ElPercha/PLsi/hard/CPU/v0/board/pictures/PLsi_00.jpg

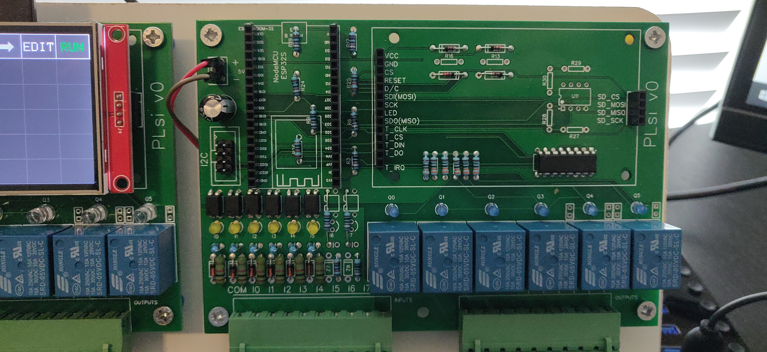
hard/CPU/v0/board/pictures/PLsi_00.jpg
