ElPercha/PLsi/hard/CPU/v0/board/pictures/PLsi_01.jpg

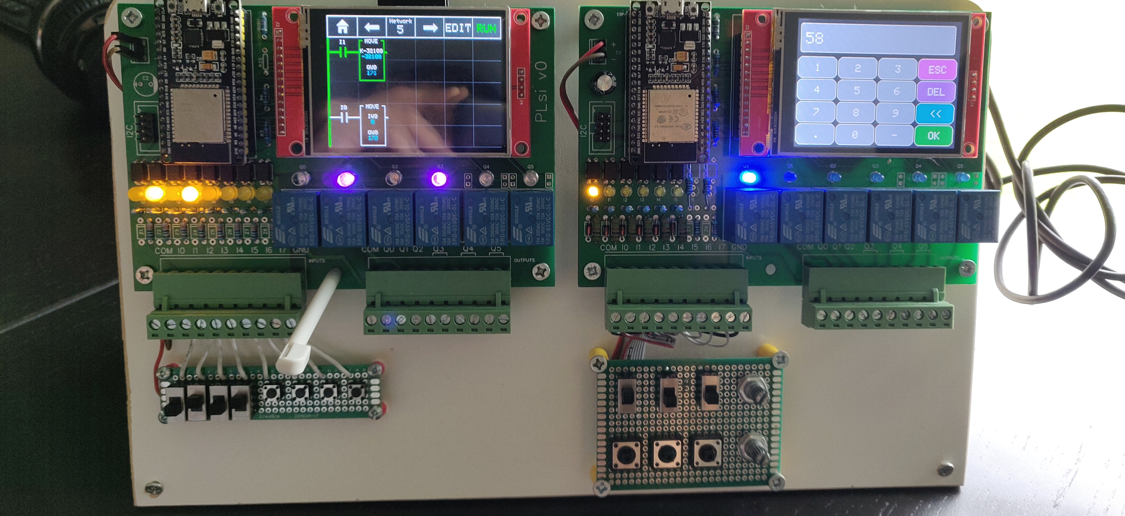
hard/CPU/v0/board/pictures/PLsi_01.jpg
