ElPercha/PLsi/hard/CPU/v0/board/pictures/PLsi_02.jpg

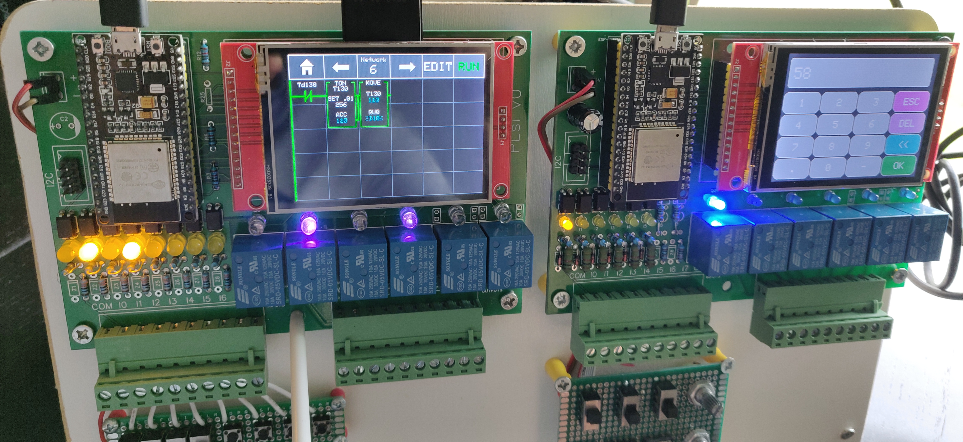
hard/CPU/v0/board/pictures/PLsi_02.jpg
