ElPercha/PLsi/hard/CPU/v0/board/pictures/PLsi_03.jpg

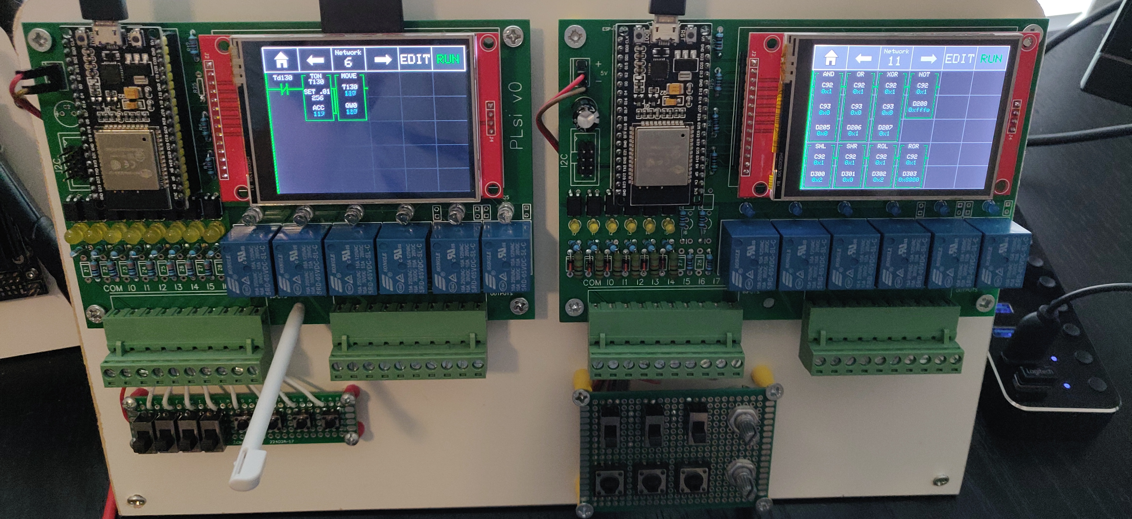
hard/CPU/v0/board/pictures/PLsi_03.jpg
