ElPercha/PLsi/hard/CPU/v0/housing/pictures/1.png

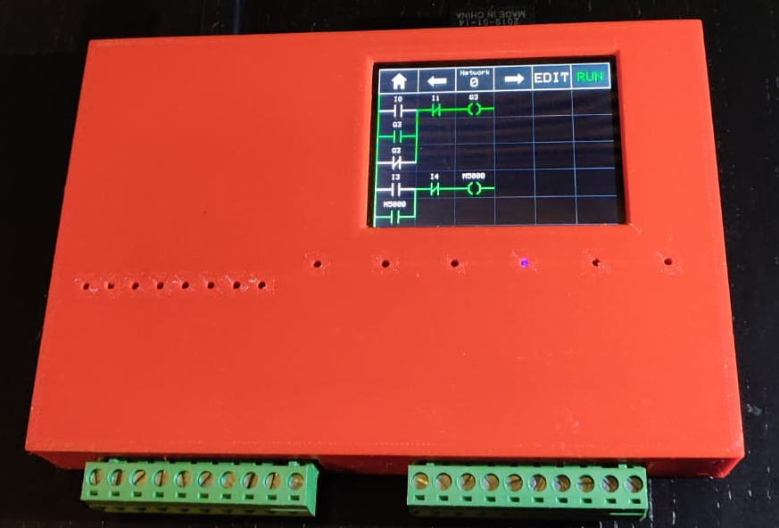
hard/CPU/v0/housing/pictures/1.png
