ElPercha/PLsi/hard/CPU/v0/housing/pictures/2.png

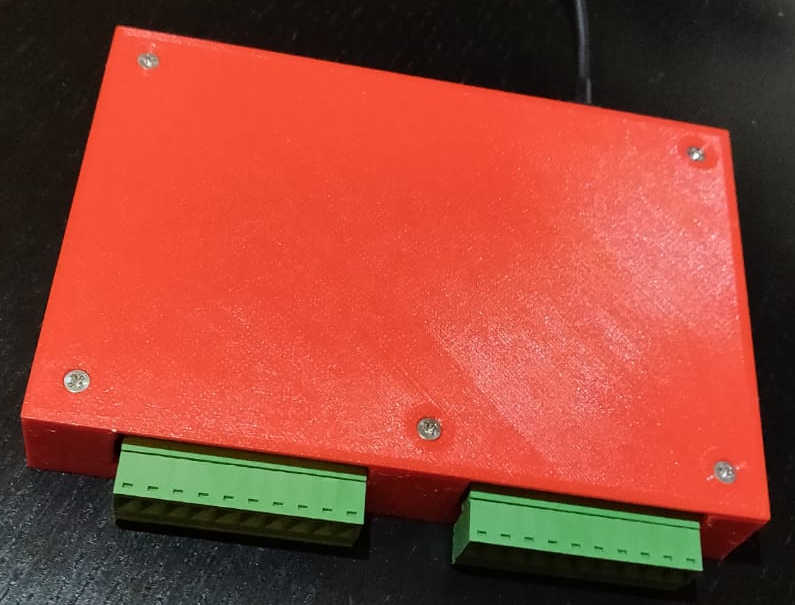
hard/CPU/v0/housing/pictures/2.png
