ElPercha/PLsi/hard/CPU/v0/housing/pictures/3.png

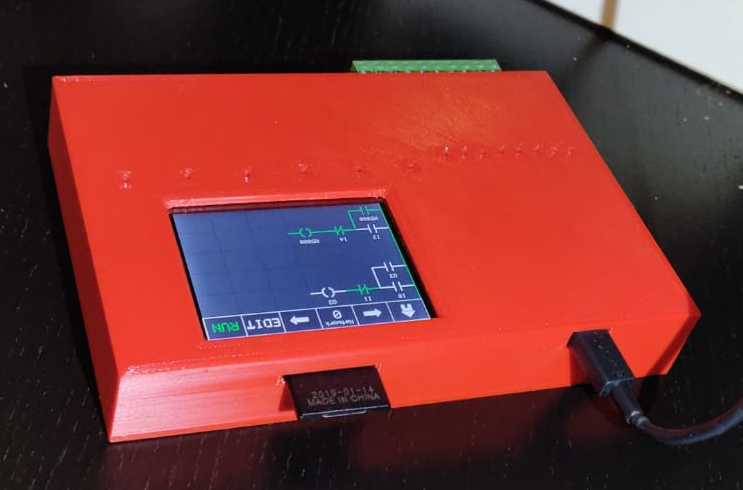
hard/CPU/v0/housing/pictures/3.png
