ElPercha/PLsi/hard/CPU/v0/housing/pictures/4.png

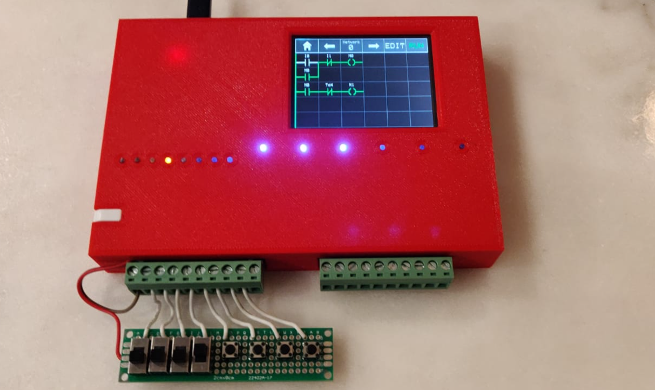
hard/CPU/v0/housing/pictures/4.png
