ElPercha/PLsi/hard/CPU/v0/housing/pictures/din rail mount 2.png

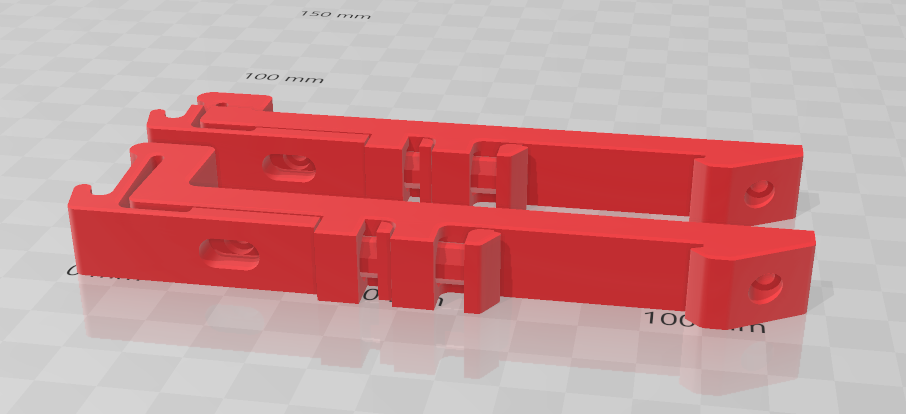
hard/CPU/v0/housing/pictures/din rail mount 2.png
