ElPercha/PLsi/hard/CPU/v0/housing/pictures/PLsi v0 - Board.png

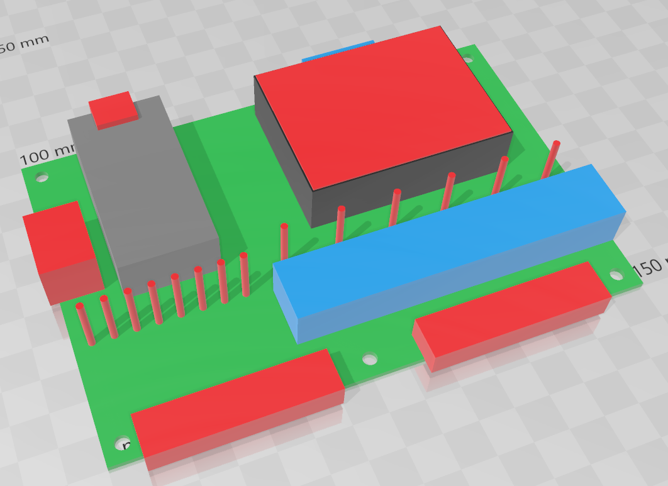
hard/CPU/v0/housing/pictures/PLsi v0 - Board.png
