ElPercha/PLsi/hard/CPU/v0/housing/pictures/PLsi v0 - Housing Base.png

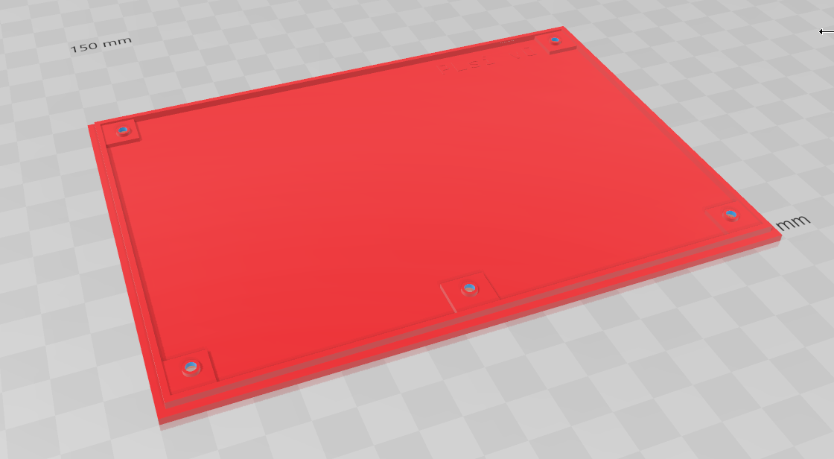
hard/CPU/v0/housing/pictures/PLsi v0 - Housing Base.png
