ElPercha/PLsi/hard/CPU/v0/housing/pictures/PLsi v0 - Housing Cover with Touch Pen.png

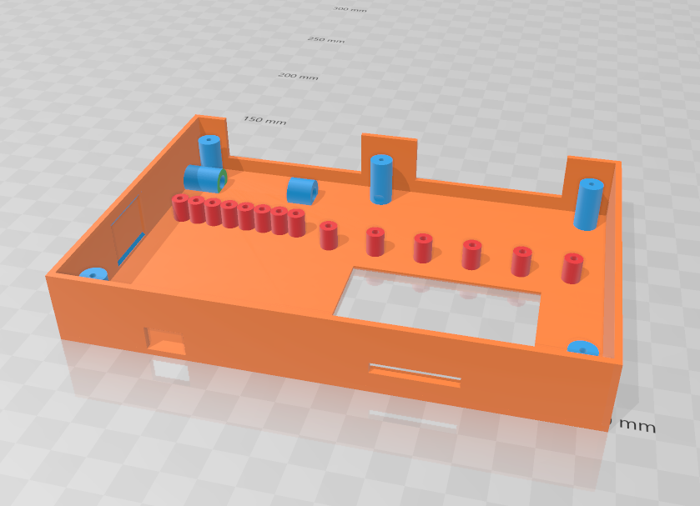
hard/CPU/v0/housing/pictures/PLsi v0 - Housing Cover with Touch Pen.png
