ElPercha/PLsi/doc/ongoing/Auxiliars/pictures for manuals/Assembly pictures/1 - Materials/1.jpeg

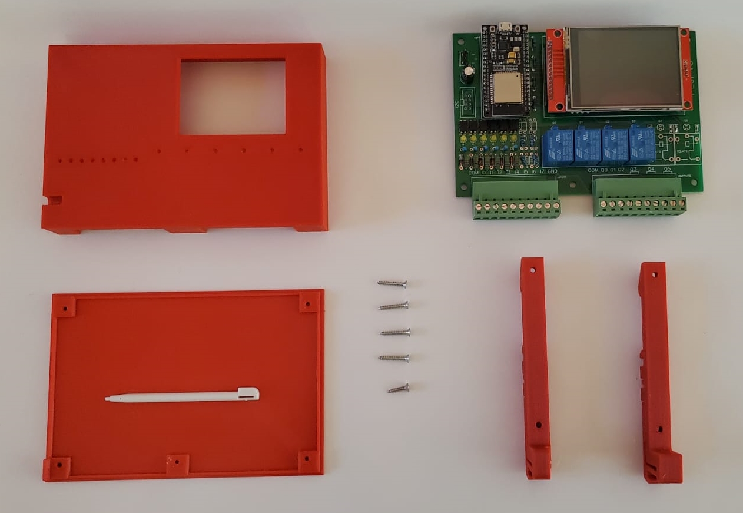
doc/ongoing/Auxiliars/pictures for manuals/Assembly pictures/1 - Materials/1.jpeg
