ElPercha/PLsi/doc/ongoing/Auxiliars/pictures for manuals/Assembly pictures/1 - Materials/2.jpeg

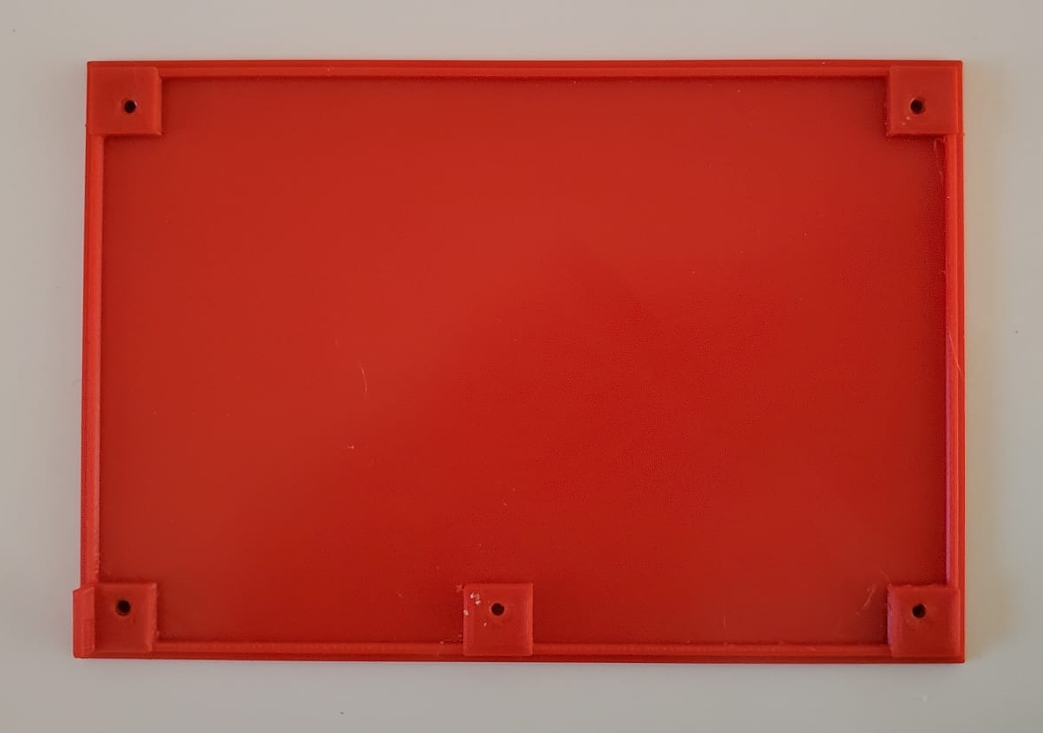
doc/ongoing/Auxiliars/pictures for manuals/Assembly pictures/1 - Materials/2.jpeg
