ElPercha/PLsi/doc/ongoing/Auxiliars/pictures for manuals/Assembly pictures/1 - Materials/4.jpeg

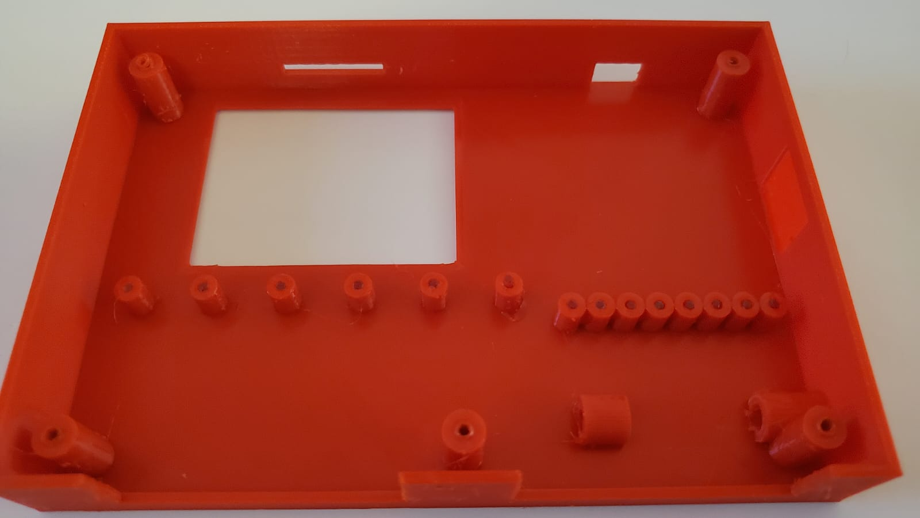
doc/ongoing/Auxiliars/pictures for manuals/Assembly pictures/1 - Materials/4.jpeg
