ElPercha/PLsi/doc/ongoing/Auxiliars/pictures for manuals/Assembly pictures/1 - Materials/5.jpeg

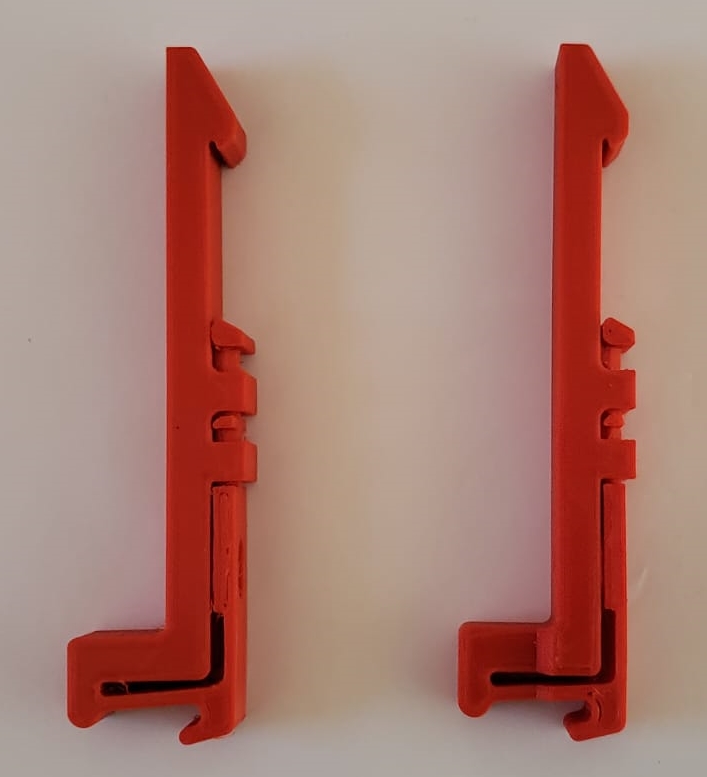
doc/ongoing/Auxiliars/pictures for manuals/Assembly pictures/1 - Materials/5.jpeg
