ElPercha/PLsi/doc/ongoing/Auxiliars/pictures for manuals/1.png

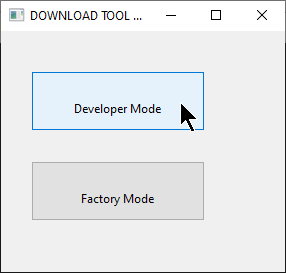
doc/ongoing/Auxiliars/pictures for manuals/1.png
