ElPercha/PLsi/doc/ongoing/Auxiliars/pictures for manuals/3.png

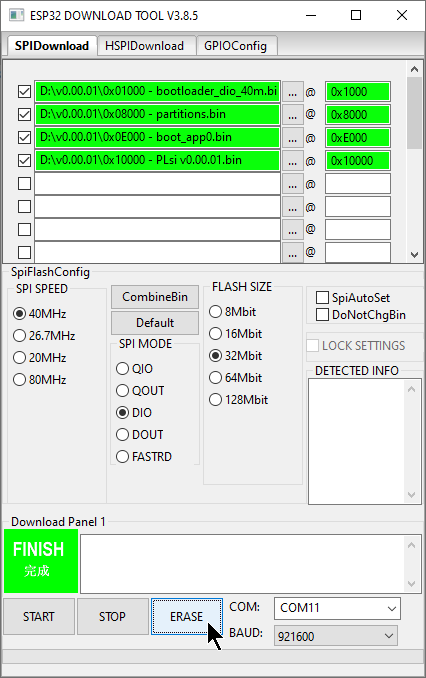
doc/ongoing/Auxiliars/pictures for manuals/3.png
