ElPercha/PLsi/doc/ongoing/Auxiliars/pictures for manuals/4.png

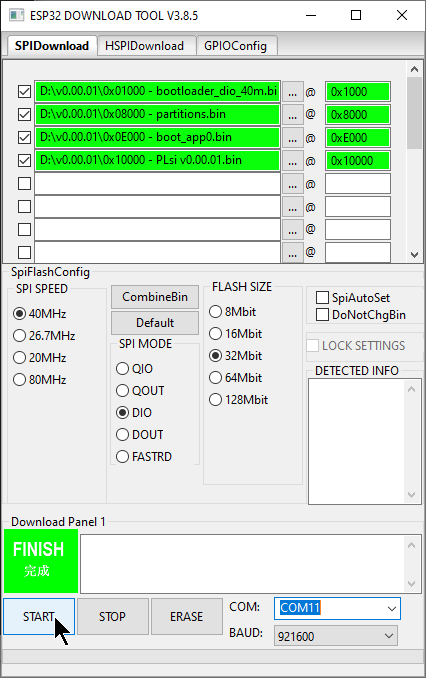
doc/ongoing/Auxiliars/pictures for manuals/4.png
