ElPercha/PLsi/doc/ongoing/Auxiliars/pictures for manuals/5.png

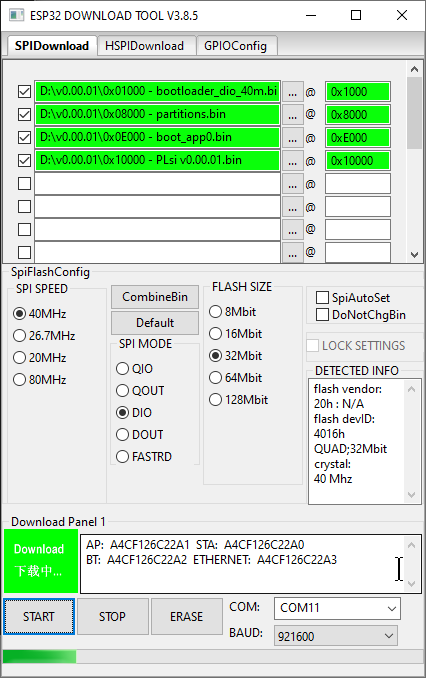
doc/ongoing/Auxiliars/pictures for manuals/5.png
