ElPercha/PLsi/doc/ongoing/Auxiliars/pictures for manuals/6.png

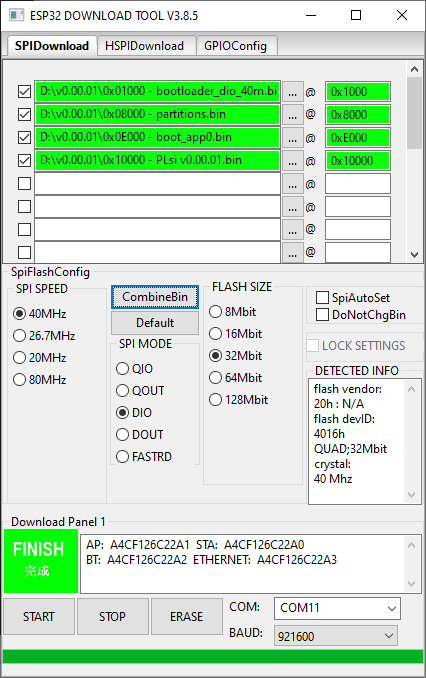
doc/ongoing/Auxiliars/pictures for manuals/6.png
