ElPercha/PLsi/doc/ongoing/Auxiliars/pictures for manuals/ADC_10Bit.png

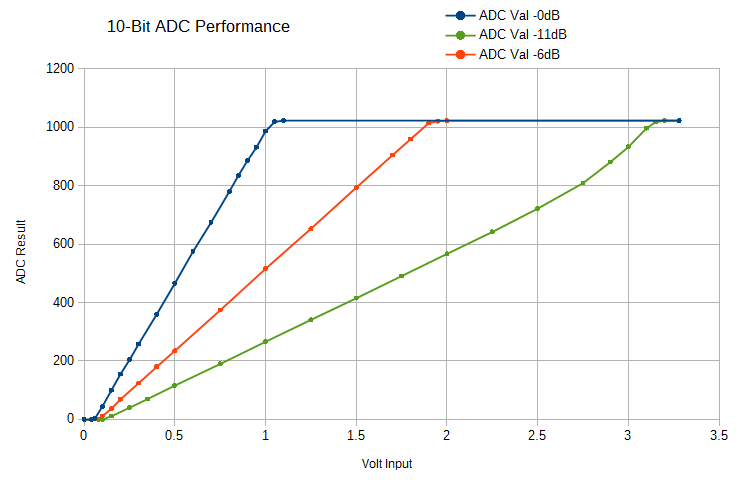
doc/ongoing/Auxiliars/pictures for manuals/ADC_10Bit.png
