ElPercha/PLsi/doc/ongoing/Auxiliars/pictures for manuals/analog unl2003 detail.PNG

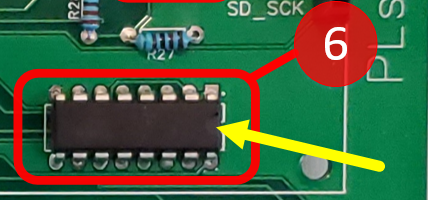
doc/ongoing/Auxiliars/pictures for manuals/analog unl2003 detail.PNG
