ElPercha/PLsi/doc/ongoing/Auxiliars/pictures for manuals/analogdivider.PNG

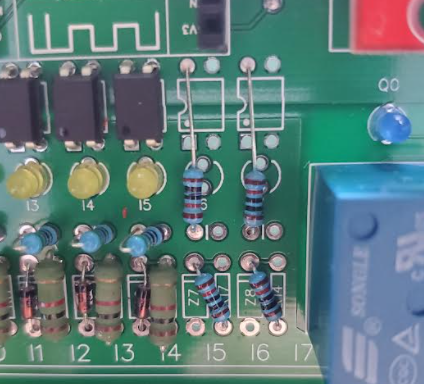
doc/ongoing/Auxiliars/pictures for manuals/analogdivider.PNG
