ElPercha/PLsi/doc/ongoing/Auxiliars/pictures for manuals/Assembly pictures/2 - Acrylic bars/5.jpeg

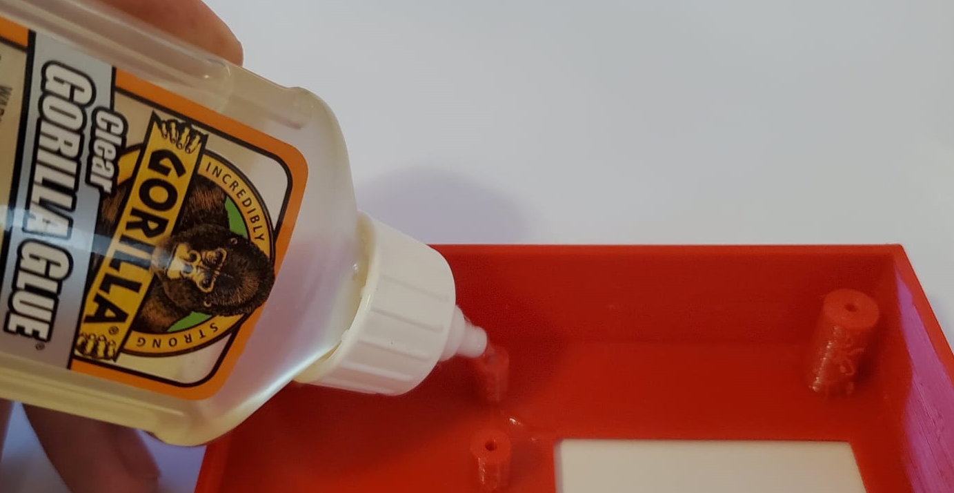
doc/ongoing/Auxiliars/pictures for manuals/Assembly pictures/2 - Acrylic bars/5.jpeg
