ElPercha/PLsi/doc/ongoing/Auxiliars/pictures for manuals/Assembly pictures/3 - assembly/4.jpeg

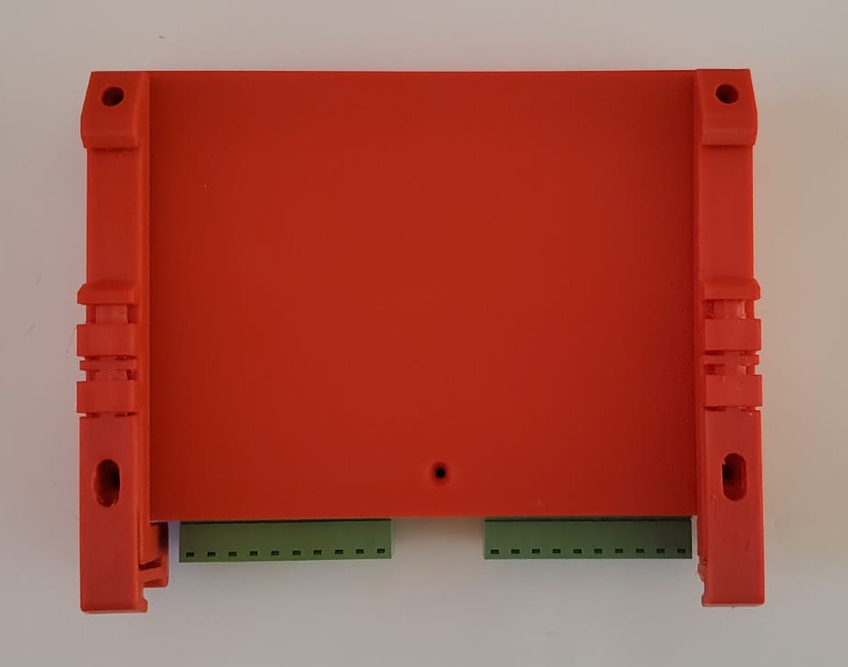
doc/ongoing/Auxiliars/pictures for manuals/Assembly pictures/3 - assembly/4.jpeg
