ElPercha/PLsi/doc/ongoing/Auxiliars/pictures for manuals/auxV.PNG

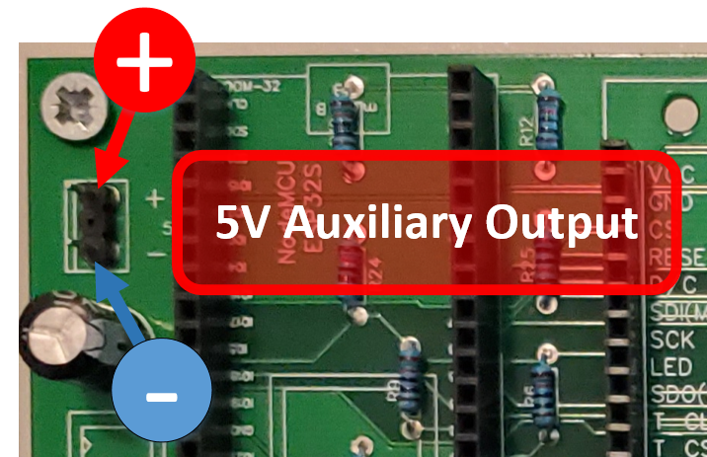
doc/ongoing/Auxiliars/pictures for manuals/auxV.PNG
