ElPercha/PLsi/doc/ongoing/Auxiliars/pictures for manuals/bar.jpg

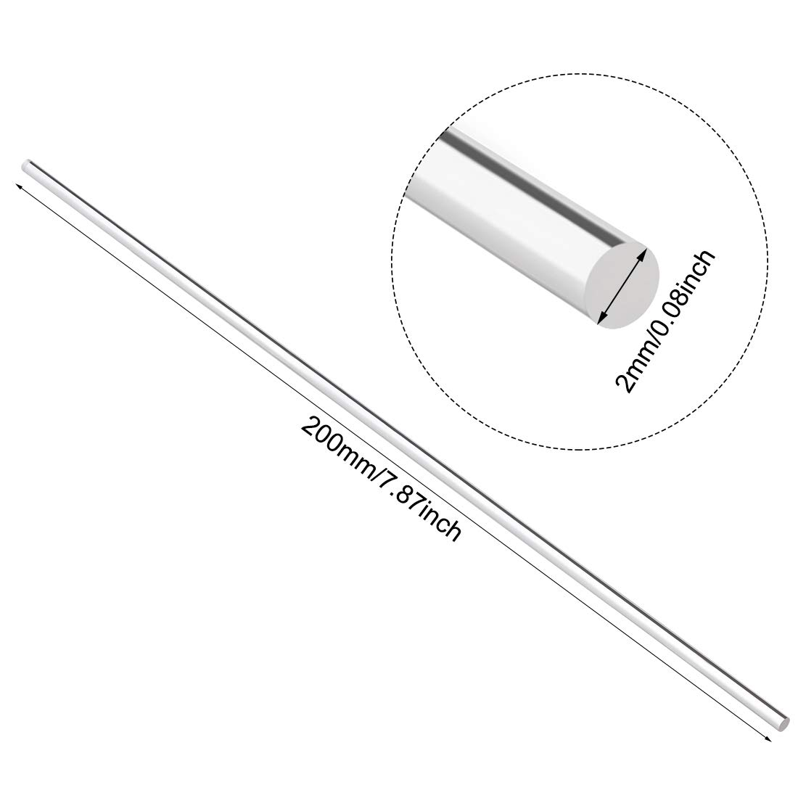
doc/ongoing/Auxiliars/pictures for manuals/bar.jpg
