ElPercha/PLsi/doc/ongoing/Auxiliars/pictures for manuals/capacitor detail.PNG

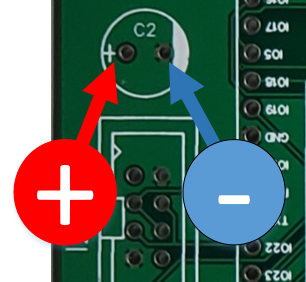
doc/ongoing/Auxiliars/pictures for manuals/capacitor detail.PNG
