ElPercha/PLsi/doc/ongoing/Auxiliars/pictures for manuals/click.png

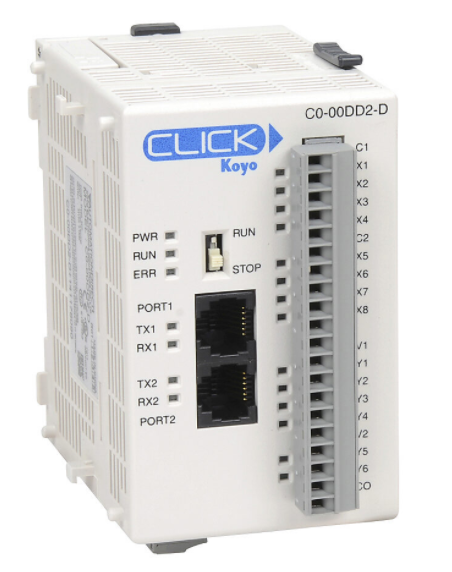
doc/ongoing/Auxiliars/pictures for manuals/click.png
