ElPercha/PLsi/doc/ongoing/Auxiliars/pictures for manuals/Dioded detail analog.PNG

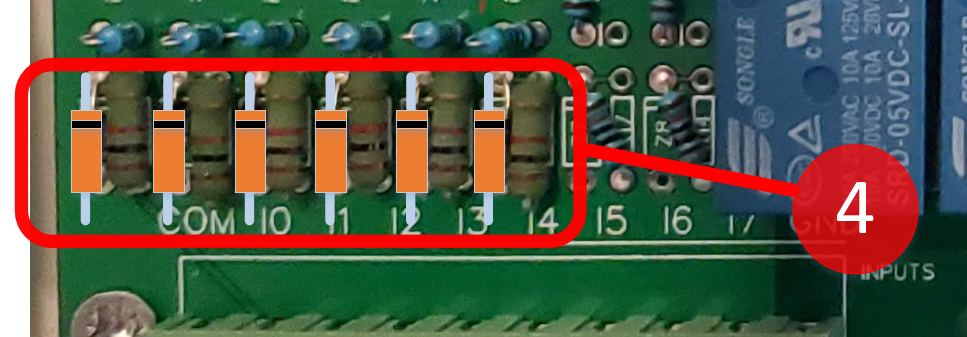
doc/ongoing/Auxiliars/pictures for manuals/Dioded detail analog.PNG
