ElPercha/PLsi/doc/ongoing/Auxiliars/pictures for manuals/Dioded detail digital.PNG

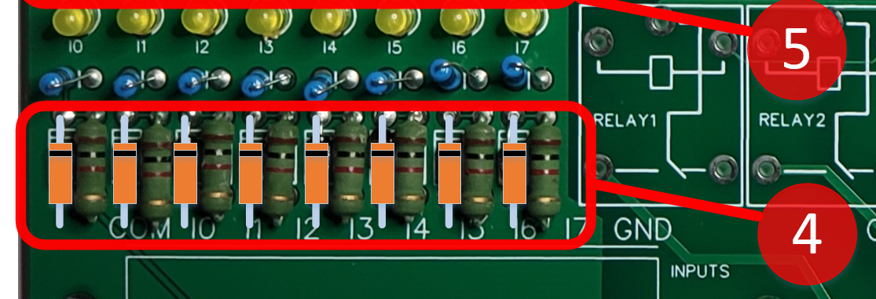
doc/ongoing/Auxiliars/pictures for manuals/Dioded detail digital.PNG
