ElPercha/PLsi/doc/ongoing/Auxiliars/pictures for manuals/Dioded detail.PNG

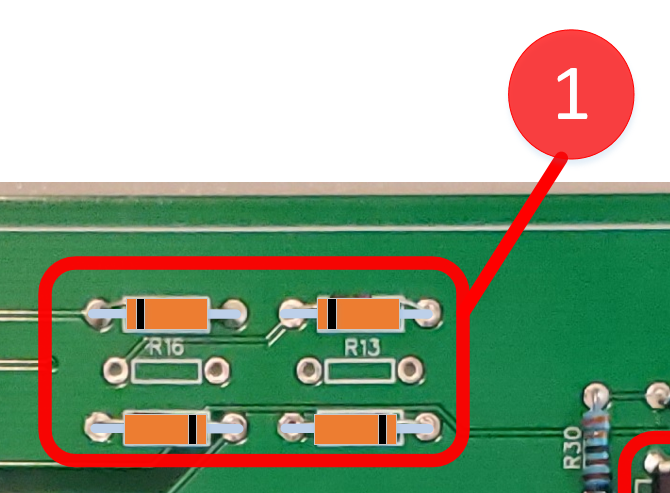
doc/ongoing/Auxiliars/pictures for manuals/Dioded detail.PNG
