ElPercha/PLsi/doc/ongoing/Auxiliars/pictures for manuals/display welding.PNG

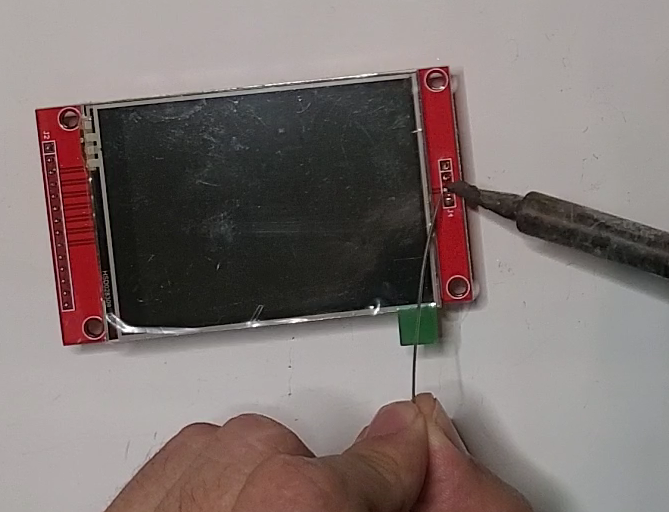
doc/ongoing/Auxiliars/pictures for manuals/display welding.PNG
