ElPercha/PLsi/doc/ongoing/Auxiliars/pictures for manuals/download2.PNG

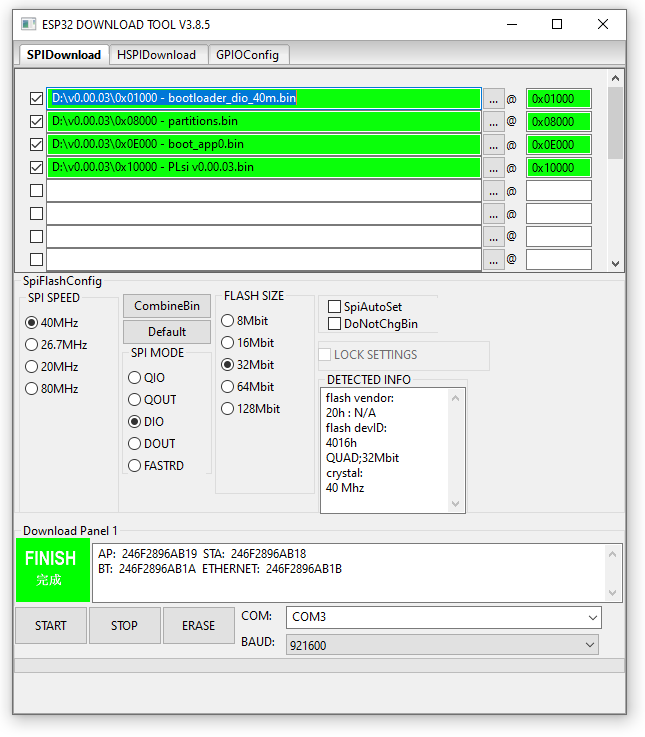
doc/ongoing/Auxiliars/pictures for manuals/download2.PNG
