ElPercha/PLsi/doc/ongoing/Auxiliars/pictures for manuals/download3.PNG

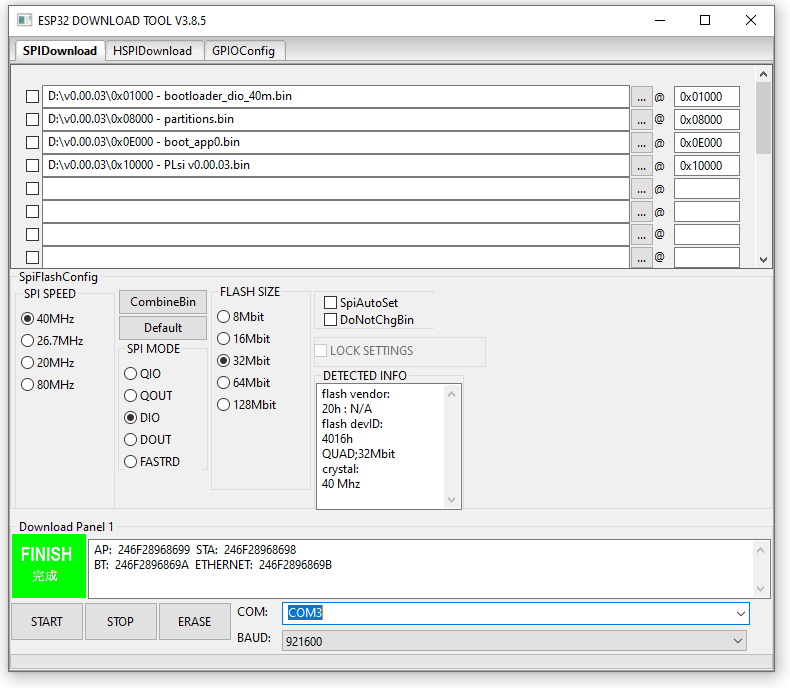
doc/ongoing/Auxiliars/pictures for manuals/download3.PNG
