ElPercha/PLsi/doc/ongoing/Auxiliars/pictures for manuals/download4.PNG

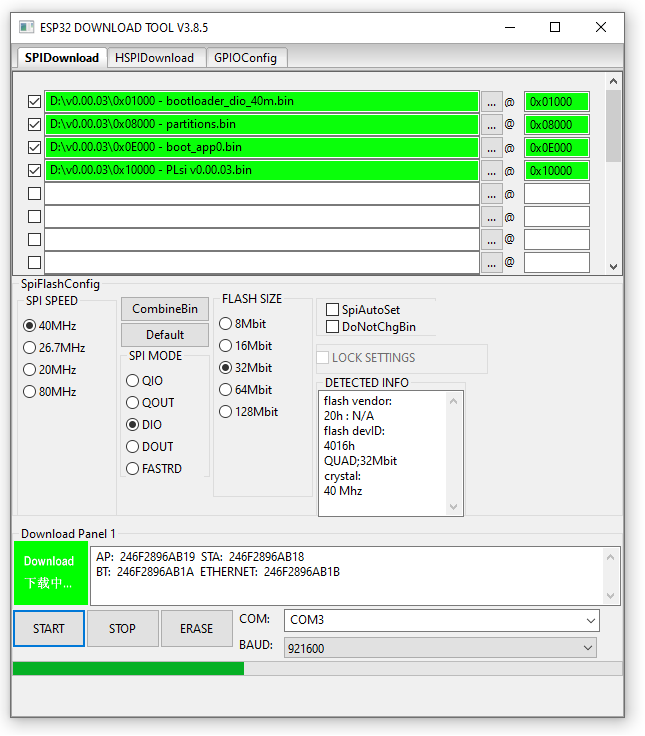
doc/ongoing/Auxiliars/pictures for manuals/download4.PNG
