ElPercha/PLsi/doc/ongoing/Auxiliars/pictures for manuals/download5.PNG

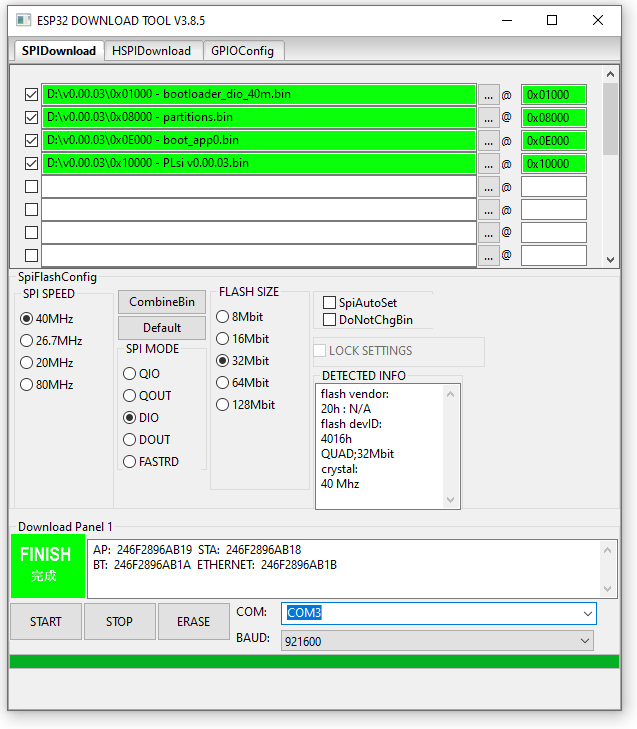
doc/ongoing/Auxiliars/pictures for manuals/download5.PNG
