ElPercha/PLsi/doc/ongoing/Auxiliars/pictures for manuals/download6.PNG

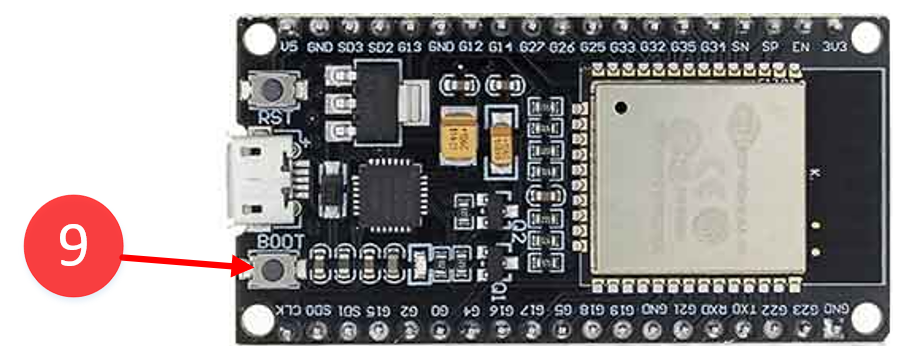
doc/ongoing/Auxiliars/pictures for manuals/download6.PNG
