ElPercha/PLsi/doc/ongoing/Auxiliars/pictures for manuals/download7.PNG

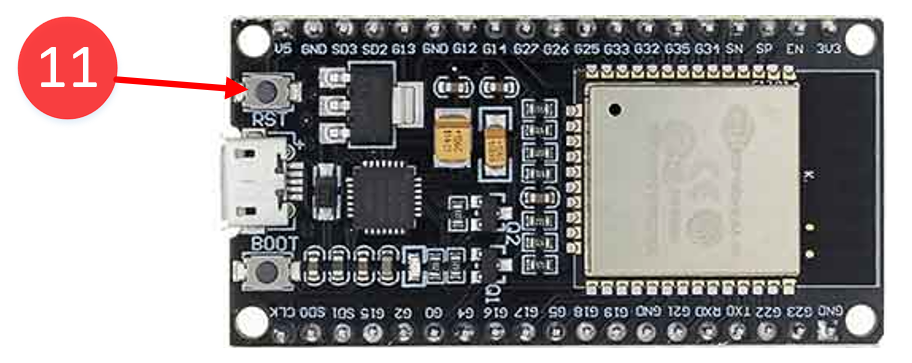
doc/ongoing/Auxiliars/pictures for manuals/download7.PNG
