ElPercha/PLsi/doc/ongoing/Auxiliars/pictures for manuals/download espressiff.PNG

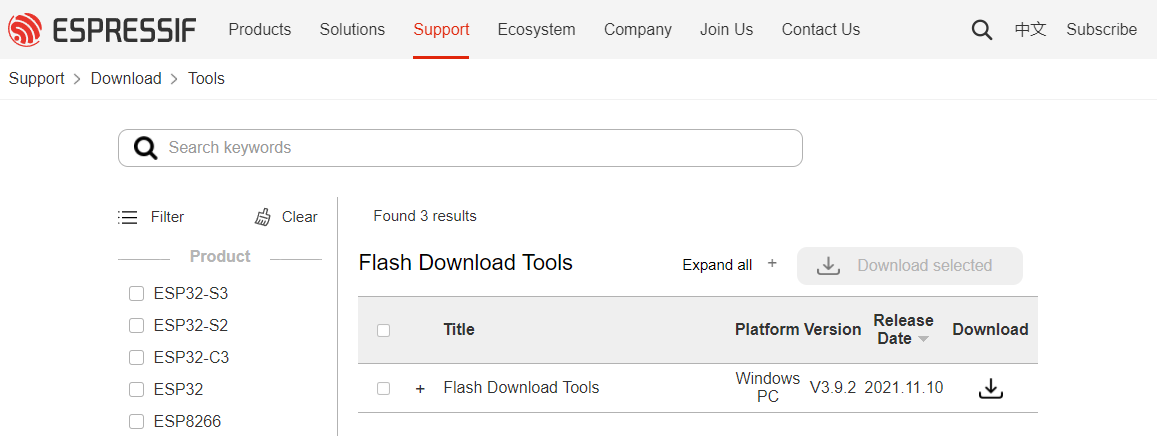
doc/ongoing/Auxiliars/pictures for manuals/download espressiff.PNG
