ElPercha/PLsi/doc/ongoing/Auxiliars/pictures for manuals/download tool.PNG

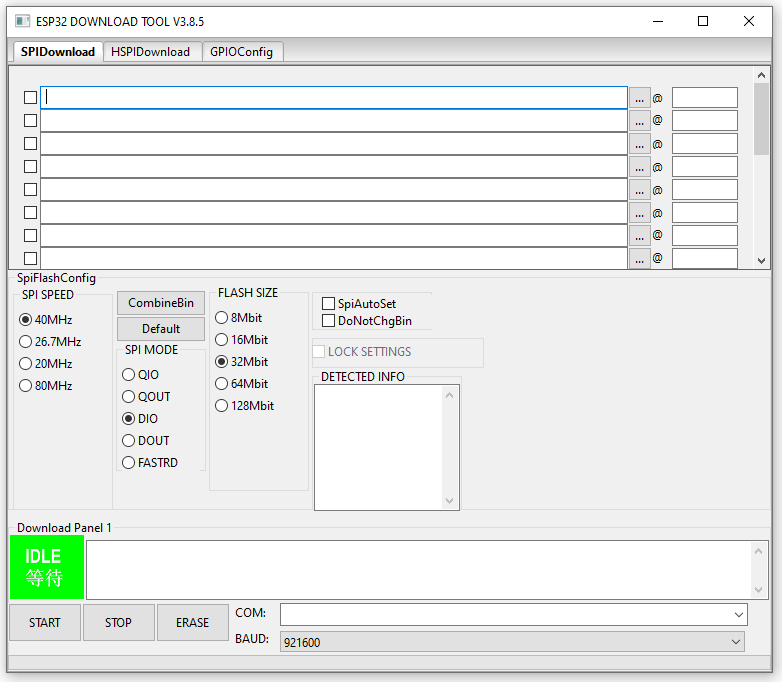
doc/ongoing/Auxiliars/pictures for manuals/download tool.PNG
