ElPercha/PLsi/doc/ongoing/Auxiliars/pictures for manuals/drawing 1.PNG

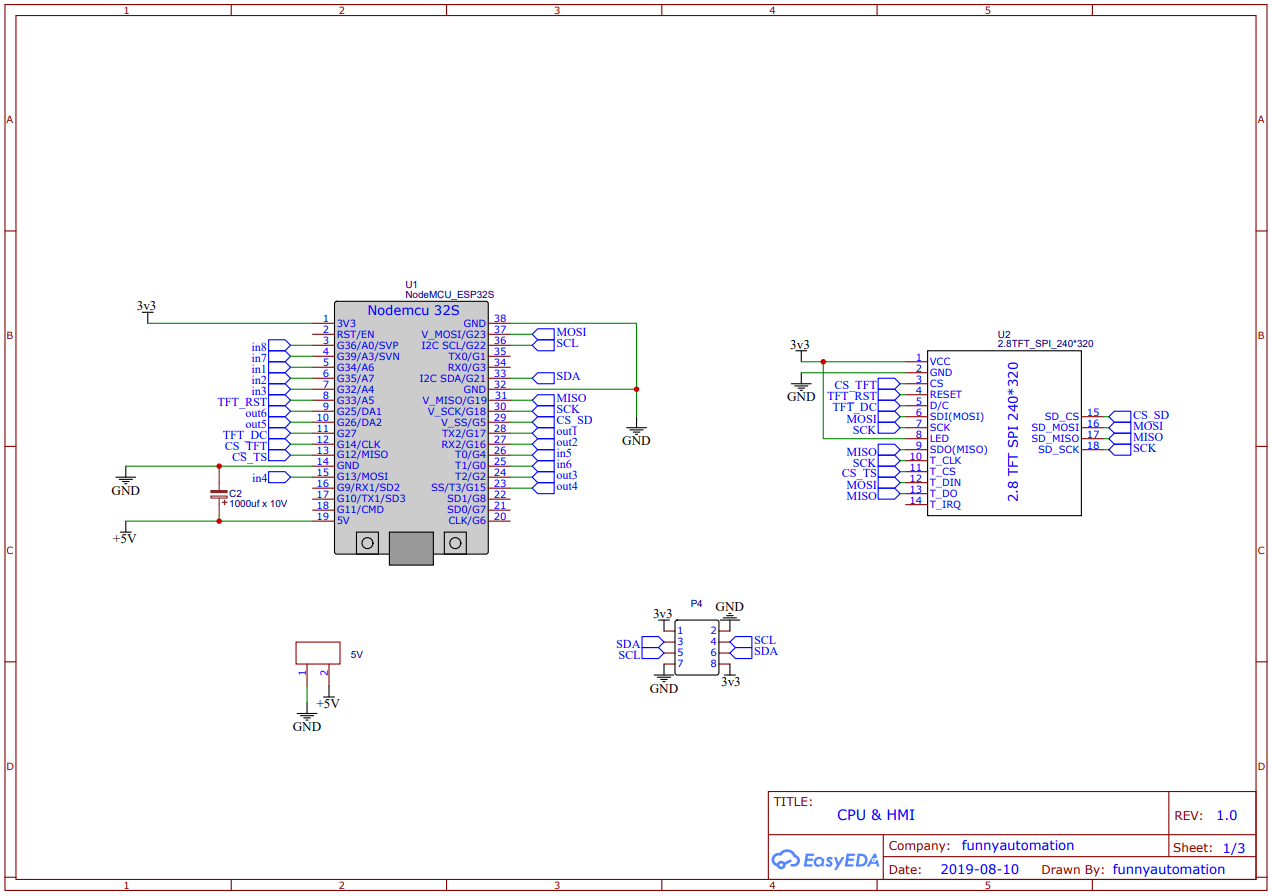
doc/ongoing/Auxiliars/pictures for manuals/drawing 1.PNG
