ElPercha/PLsi/doc/ongoing/Auxiliars/pictures for manuals/drawing 3.PNG

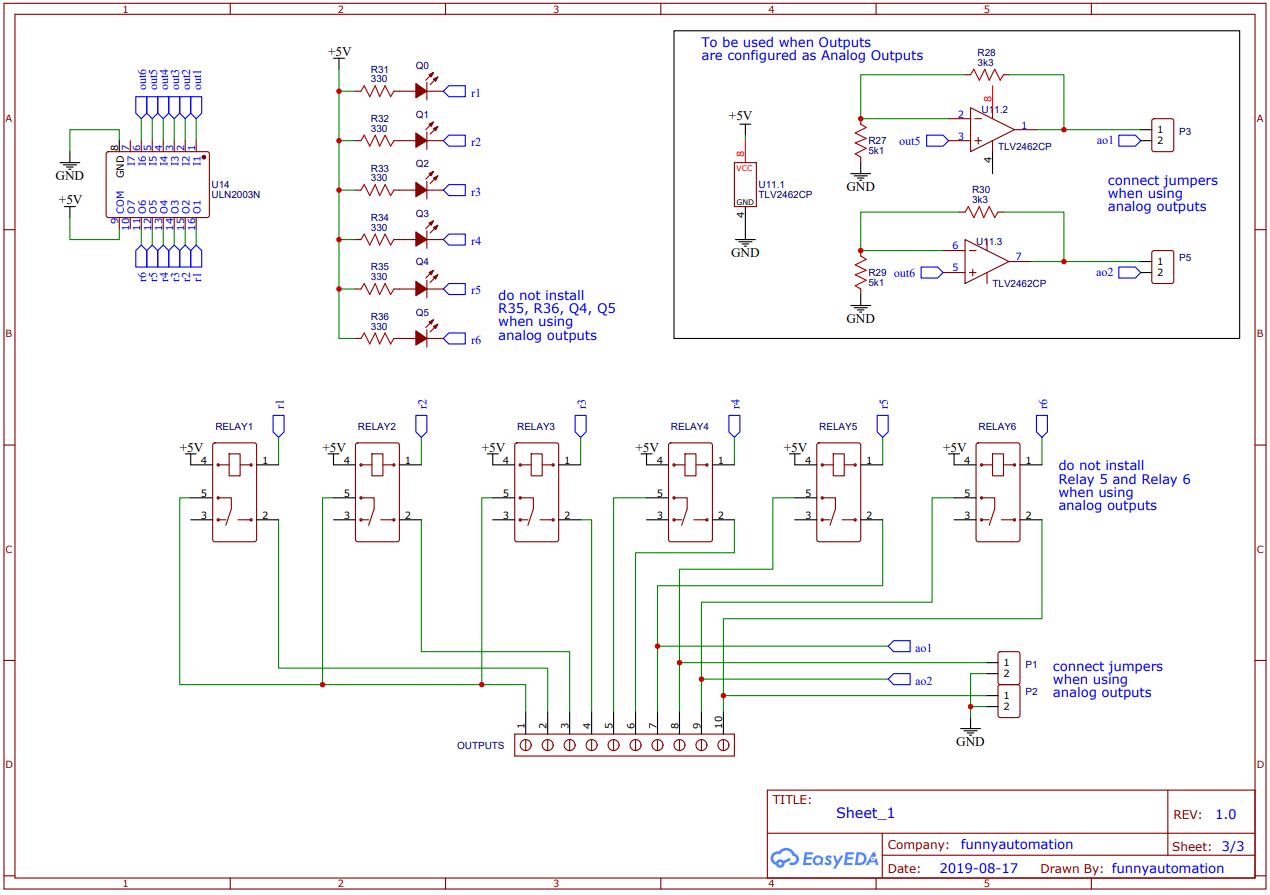
doc/ongoing/Auxiliars/pictures for manuals/drawing 3.PNG
