ElPercha/PLsi/doc/ongoing/Auxiliars/pictures for manuals/dupont female1.PNG

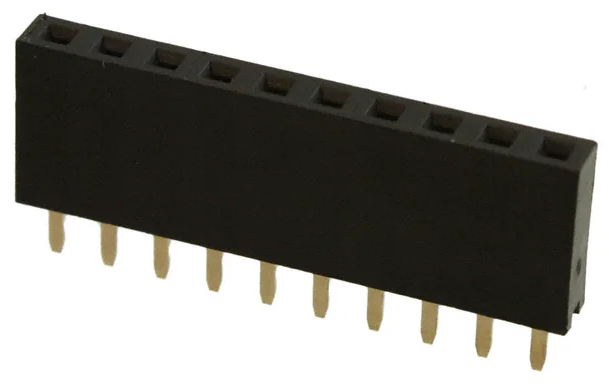
doc/ongoing/Auxiliars/pictures for manuals/dupont female1.PNG
