ElPercha/PLsi/doc/ongoing/Auxiliars/pictures for manuals/dupont female.PNG

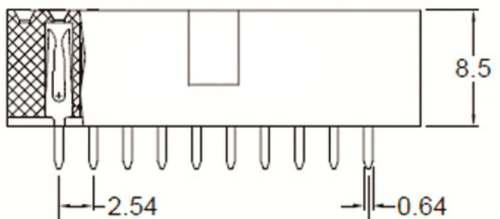
doc/ongoing/Auxiliars/pictures for manuals/dupont female.PNG
