ElPercha/PLsi/doc/ongoing/Auxiliars/pictures for manuals/esp32.PNG

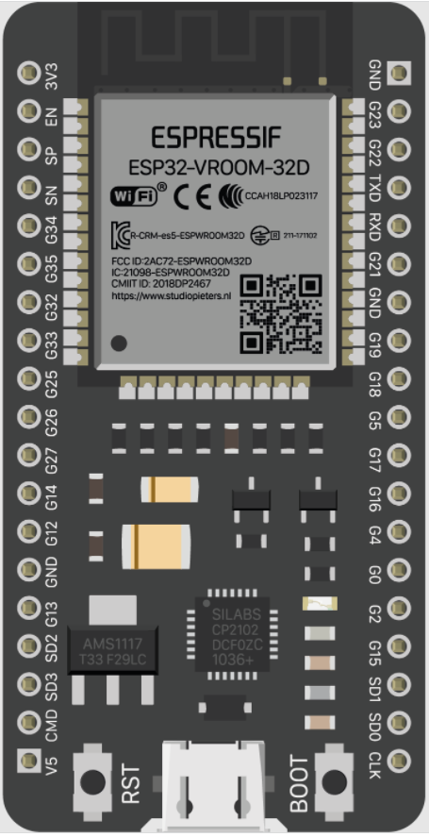
doc/ongoing/Auxiliars/pictures for manuals/esp32.PNG
