ElPercha/PLsi/doc/ongoing/Auxiliars/pictures for manuals/esp321.PNG

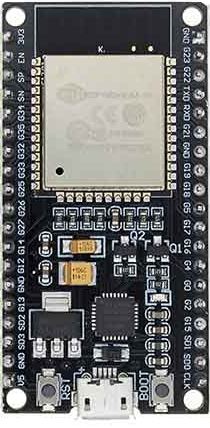
doc/ongoing/Auxiliars/pictures for manuals/esp321.PNG
