ElPercha/PLsi/doc/ongoing/Auxiliars/pictures for manuals/espressif.png

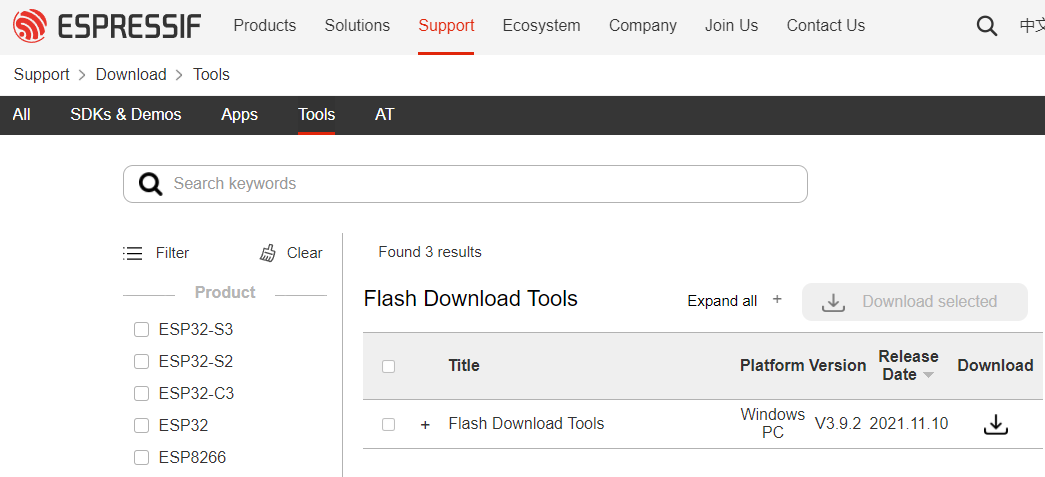
doc/ongoing/Auxiliars/pictures for manuals/espressif.png
