ElPercha/PLsi/doc/ongoing/Auxiliars/pictures for manuals/flashtool.PNG

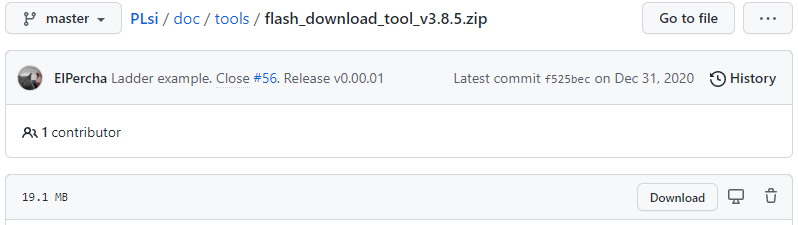
doc/ongoing/Auxiliars/pictures for manuals/flashtool.PNG
