ElPercha/PLsi/doc/ongoing/Auxiliars/pictures for manuals/led.PNG

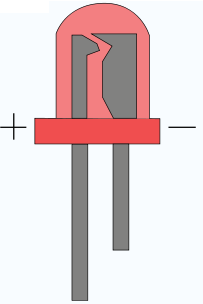
doc/ongoing/Auxiliars/pictures for manuals/led.PNG
