ElPercha/PLsi/doc/ongoing/Auxiliars/pictures for manuals/opamp detail.PNG

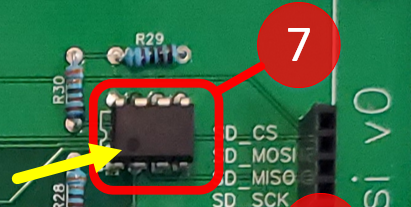
doc/ongoing/Auxiliars/pictures for manuals/opamp detail.PNG
