ElPercha/PLsi/doc/ongoing/Auxiliars/pictures for manuals/optionsdigital.PNG

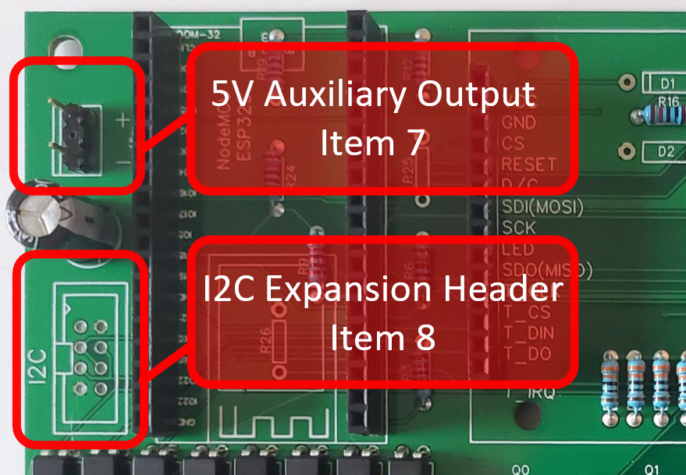
doc/ongoing/Auxiliars/pictures for manuals/optionsdigital.PNG
