ElPercha/PLsi/doc/ongoing/Auxiliars/pictures for manuals/optoanalogdetail.PNG

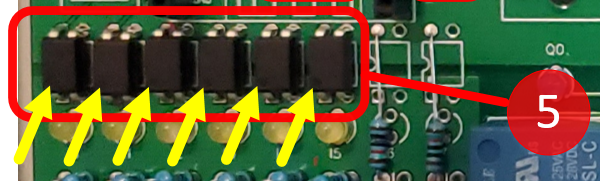
doc/ongoing/Auxiliars/pictures for manuals/optoanalogdetail.PNG
