ElPercha/PLsi/doc/ongoing/Auxiliars/pictures for manuals/PC817 Details.PNG

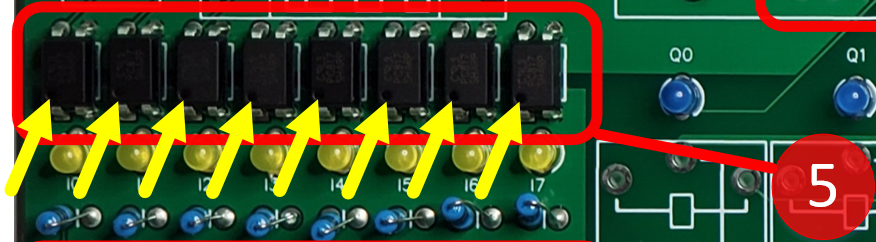
doc/ongoing/Auxiliars/pictures for manuals/PC817 Details.PNG
