ElPercha/PLsi/doc/ongoing/Auxiliars/pictures for manuals/plsi flash tool.PNG

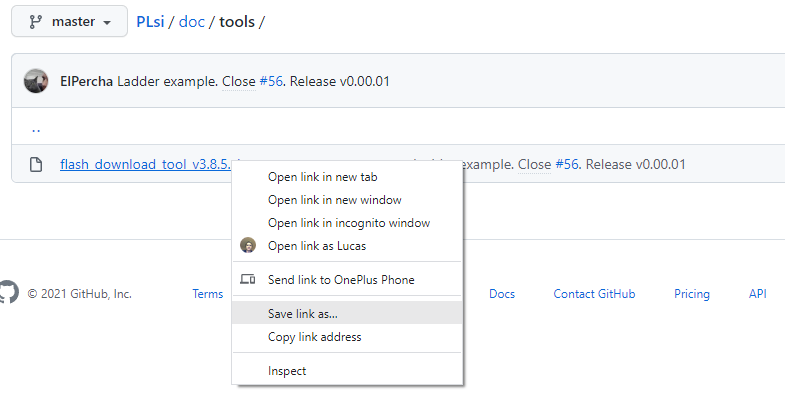
doc/ongoing/Auxiliars/pictures for manuals/plsi flash tool.PNG
