ElPercha/PLsi/doc/ongoing/Auxiliars/pictures for manuals/screw1.png

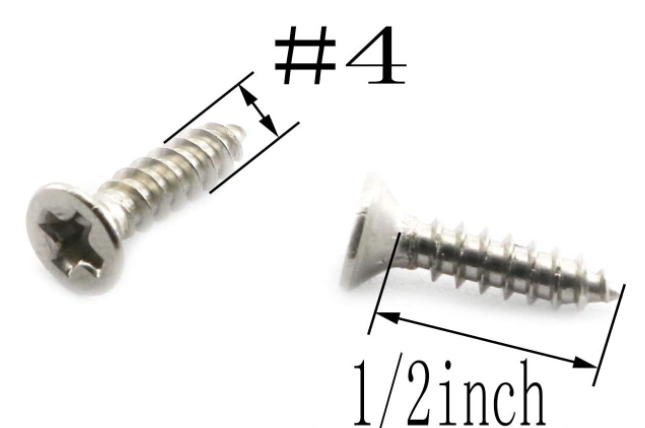
doc/ongoing/Auxiliars/pictures for manuals/screw1.png
