ElPercha/PLsi/doc/ongoing/Auxiliars/pictures for manuals/UNL2003 detail.PNG

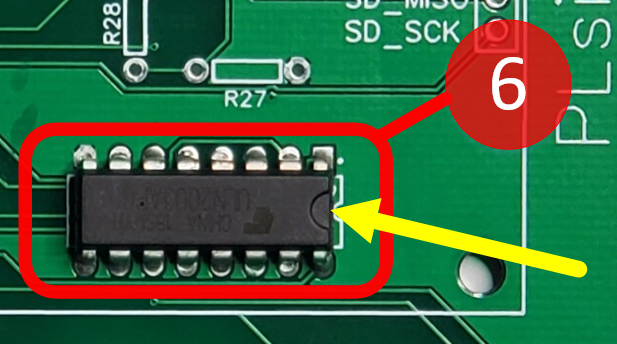
doc/ongoing/Auxiliars/pictures for manuals/UNL2003 detail.PNG
