ElPercha/PLsi/doc/ongoing/Auxiliars/pictures for manuals/unzip.PNG

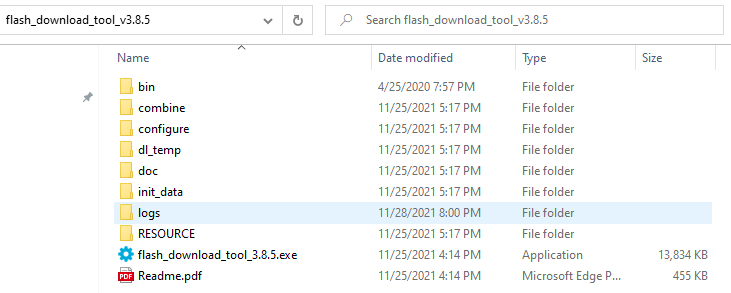
doc/ongoing/Auxiliars/pictures for manuals/unzip.PNG
