ElPercha/PLsi/doc/ongoing/Auxiliars/UserManualScreenShoots/1 - Ladder/4 - Instructions/7 - U/U 1.png

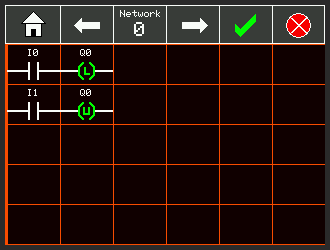
doc/ongoing/Auxiliars/UserManualScreenShoots/1 - Ladder/4 - Instructions/7 - U/U 1.png
