ElPercha/PLsi/doc/ongoing/Auxiliars/UserManualScreenShoots/1 - Ladder/4 - Instructions/8 - BAR/BAR 4.png

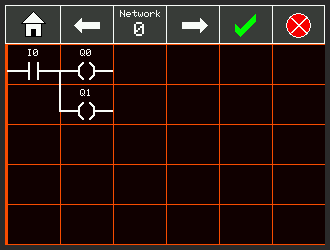
doc/ongoing/Auxiliars/UserManualScreenShoots/1 - Ladder/4 - Instructions/8 - BAR/BAR 4.png
