ElPercha/PLsi/doc/ongoing/Auxiliars/UserManualScreenShoots/2 - HMI/1.png

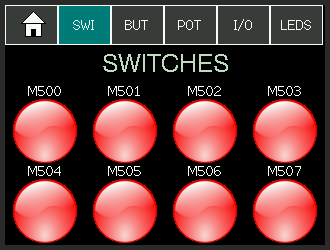
doc/ongoing/Auxiliars/UserManualScreenShoots/2 - HMI/1.png
