ElPercha/PLsi/doc/ongoing/Auxiliars/UserManualScreenShoots/2 - HMI/3.png

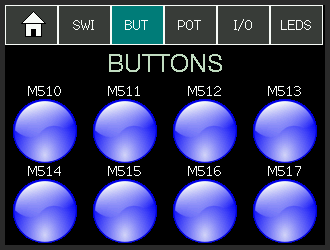
doc/ongoing/Auxiliars/UserManualScreenShoots/2 - HMI/3.png
