ElPercha/PLsi/doc/ongoing/Auxiliars/UserManualScreenShoots/2 - HMI/9.png

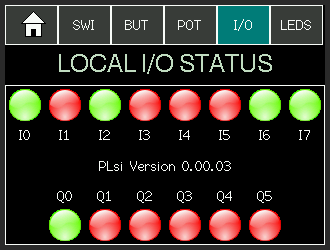
doc/ongoing/Auxiliars/UserManualScreenShoots/2 - HMI/9.png
