ElPercha/PLsi/doc/ongoing/Auxiliars/UserManualScreenShoots/2 - HMI/10.png

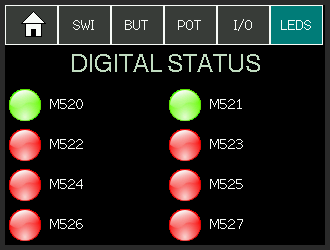
doc/ongoing/Auxiliars/UserManualScreenShoots/2 - HMI/10.png
