ElPercha/PLsi/doc/ongoing/Auxiliars/UserManualScreenShoots/3 - Configuration/1 - PLC/error1.png

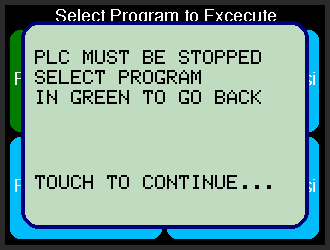
doc/ongoing/Auxiliars/UserManualScreenShoots/3 - Configuration/1 - PLC/error1.png
