ElPercha/PLsi/doc/ongoing/Auxiliars/UserManualScreenShoots/3 - Configuration/1 - PLC/program 4.png

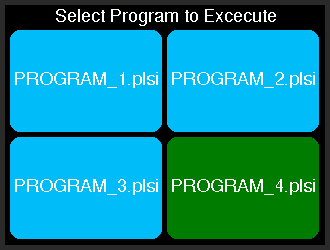
doc/ongoing/Auxiliars/UserManualScreenShoots/3 - Configuration/1 - PLC/program 4.png
