ElPercha/PLsi/doc/ongoing/Auxiliars/UserManualScreenShoots/3 - Configuration/1 - PLC/program default.png

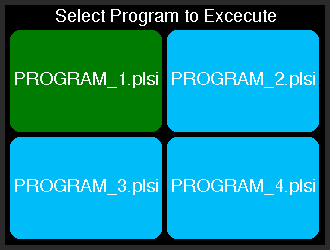
doc/ongoing/Auxiliars/UserManualScreenShoots/3 - Configuration/1 - PLC/program default.png
