ElPercha/PLsi/doc/ongoing/Auxiliars/UserManualScreenShoots/3 - Configuration/2 - HMI/hmi.png

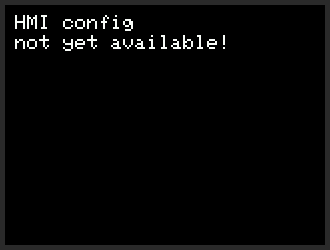
doc/ongoing/Auxiliars/UserManualScreenShoots/3 - Configuration/2 - HMI/hmi.png
