ElPercha/PLsi/doc/ongoing/Auxiliars/UserManualScreenShoots/3 - Configuration/3 - IO/error1.png

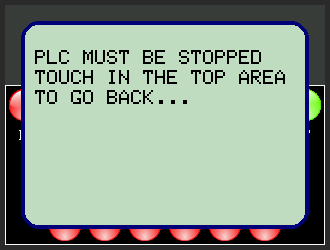
doc/ongoing/Auxiliars/UserManualScreenShoots/3 - Configuration/3 - IO/error1.png
