ElPercha/PLsi/doc/ongoing/Auxiliars/UserManualScreenShoots/3 - Configuration/3 - IO/screenshot_2021_12_26_23_4_0.png

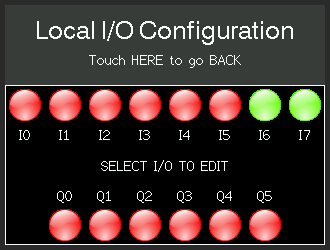
doc/ongoing/Auxiliars/UserManualScreenShoots/3 - Configuration/3 - IO/screenshot_2021_12_26_23_4_0.png
