ElPercha/PLsi/doc/ongoing/Auxiliars/UserManualScreenShoots/3 - Configuration/3 - IO/screenshot_2024_6_2_11_28_26.png

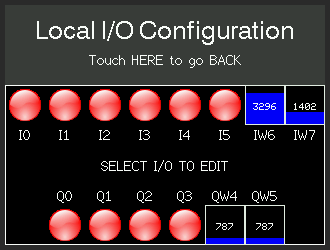
doc/ongoing/Auxiliars/UserManualScreenShoots/3 - Configuration/3 - IO/screenshot_2024_6_2_11_28_26.png
