ElPercha/PLsi/doc/ongoing/Auxiliars/UserManualScreenShoots/3 - Configuration/4 - Network/1 - WiFi/1.png

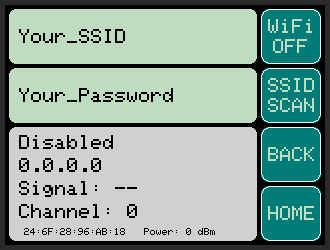
doc/ongoing/Auxiliars/UserManualScreenShoots/3 - Configuration/4 - Network/1 - WiFi/1.png
