ElPercha/PLsi/doc/ongoing/Auxiliars/UserManualScreenShoots/3 - Configuration/4 - Network/1 - WiFi/3.png

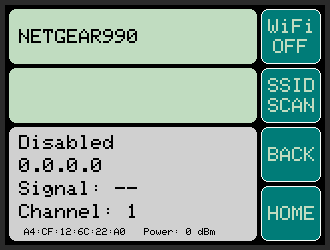
doc/ongoing/Auxiliars/UserManualScreenShoots/3 - Configuration/4 - Network/1 - WiFi/3.png
