ElPercha/PLsi/doc/ongoing/Auxiliars/UserManualScreenShoots/3 - Configuration/4 - Network/2 - modbusTCP.png

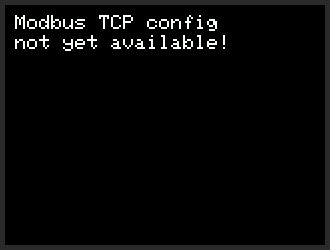
doc/ongoing/Auxiliars/UserManualScreenShoots/3 - Configuration/4 - Network/2 - modbusTCP.png
