ElPercha/PLsi/doc/ongoing/Auxiliars/UserManualScreenShoots/3 - Configuration/4 - Network/4 - network.png

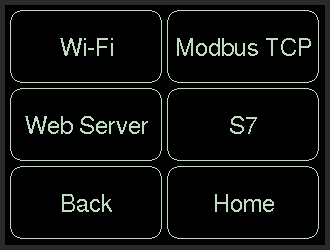
doc/ongoing/Auxiliars/UserManualScreenShoots/3 - Configuration/4 - Network/4 - network.png
