ElPercha/PLsi/doc/ongoing/Auxiliars/UserManualScreenShoots/3 - Configuration/5 - System/0a.png

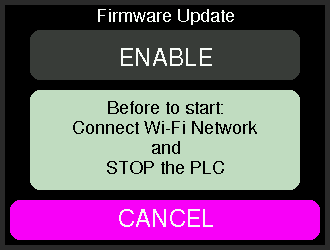
doc/ongoing/Auxiliars/UserManualScreenShoots/3 - Configuration/5 - System/0a.png
