ElPercha/PLsi/doc/ongoing/Auxiliars/UserManualScreenShoots/3 - Configuration/5 - System/1.png

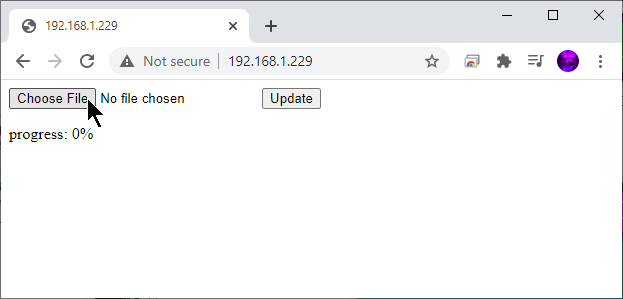
doc/ongoing/Auxiliars/UserManualScreenShoots/3 - Configuration/5 - System/1.png
