ElPercha/PLsi/doc/ongoing/Auxiliars/UserManualScreenShoots/3 - Configuration/5 - System/2a.png

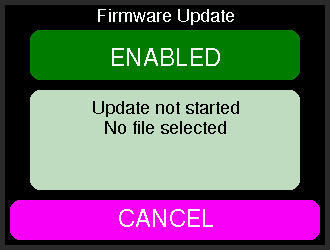
doc/ongoing/Auxiliars/UserManualScreenShoots/3 - Configuration/5 - System/2a.png
