ElPercha/PLsi/doc/ongoing/Auxiliars/UserManualScreenShoots/3 - Configuration/main.png

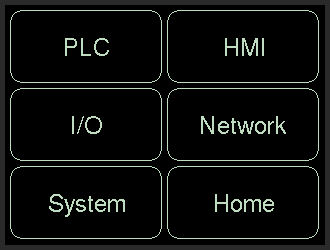
doc/ongoing/Auxiliars/UserManualScreenShoots/3 - Configuration/main.png
