ElPercha/PLsi/firm/include/buttons.h

// Copyright (c) 2019 Lucas Prieto
// Licensed under the MIT License. See LICENSE file in the project root for full license information.

#include <globals.h>
#include <pgmspace.h> // To use FLASH as storage with PROGMEM directive

// Color index of 64 x 64 pixels buttons:
//  0= red
//  1= green
//  2= blue
//  3= yellow

const unsigned short buttons64[4][4096] PROGMEM={{
0x0000, 0x0000, 0x0000, 0x0000, 0x0000, 0x0000, 0x0000, 0x0000, 0x0000, 0x0000, 0x0000, 0x0000, 0x0000, 0x0000, 0x0000, 0x0000,   // 0x0010 (16) pixels
0x0000, 0x0000, 0x0000, 0x0000, 0x0000, 0x0000, 0x0000, 0x0000, 0x0000, 0x0000, 0xD800, 0xD000, 0xD000, 0xD000, 0xD800, 0xD800,   // 0x0020 (32) pixels
0xD800, 0xD000, 0xD000, 0xD000, 0xD000, 0xC000, 0x0000, 0x0000, 0x0000, 0x0000, 0x0000, 0x0000, 0x0000, 0x0000, 0x0000, 0x0000,   // 0x0030 (48) pixels
0x0000, 0x0000, 0x0000, 0x0000, 0x0000, 0x0000, 0x0000, 0x0000, 0x0000, 0x0000, 0x0000, 0x0000, 0x0000, 0x0000, 0x0000, 0x0000,   // 0x0040 (64) pixels
0x0000, 0x0000, 0x0000, 0x0000, 0x0000, 0x0000, 0x0000, 0x0000, 0x0000, 0x0000, 0x0000, 0x0000, 0x0000, 0x0000, 0x0000, 0x0000,   // 0x0050 (80) pixels
0x0000, 0x0000, 0x0000, 0x0000, 0x0000, 0x0000, 0xD000, 0xD000, 0xD800, 0xD800, 0xD800, 0xE000, 0xE800, 0xE800, 0xF000, 0xF000,   // 0x0060 (96) pixels
0xF000, 0xF000, 0xE800, 0xE800, 0xE000, 0xD800, 0xD800, 0xD800, 0xD000, 0xD800, 0x0000, 0x0000, 0x0000, 0x0000, 0x0000, 0x0000,   // 0x0070 (112) pixels
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
0x0000, 0x0000, 0x0000, 0x0000, 0x0000, 0x0000, 0x0000, 0x0000, 0x0000, 0x0000, 0x0000, 0x0000, 0x0000, 0x0000, 0x0000, 0x0000,   // 0x1000 (4096) pixels
}
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
