ElPercha/PLsi/firm/include/ladder.h

// Copyright (c) 2019 Lucas Prieto
// Licensed under the MIT License. See LICENSE file in the project root for full license information.

#ifndef LADDER_H
#define LADDER_H

//--------------------------------------------------------------------------------
// Globals variables for Ladder 
//--------------------------------------------------------------------------------

extern uint16_t NetworkFlags[NET_COLUMNS - 1];
extern unsigned long actualScanTime;
extern unsigned long startTime;
extern uint16_t analogInFilter[IO_LOCAL_IN_ANALOG_QTY][ANALOG_FILTER_SAMPLES]; 
extern uint16_t analogInFilterPointer[IO_LOCAL_IN_ANALOG_QTY];

//--------------------------------------------------------------------------------
// Globals variables from other tasks
//--------------------------------------------------------------------------------

extern uint16_t NetworkFlagsOnline [NET_COLUMNS - 1];
extern uint16_t editionMode;

//--------------------------------------------------------------------------------
// PLC Scan main functions
//--------------------------------------------------------------------------------

void ladderWaitSettings(void);

void configureLocal_IO(void);
uint16_t analogInfilter(uint16_t index, uint16_t value);
void clearMemory(void);

void readInputsLocal(void);
void readInputsRemote(void);

void scanTime(void);
void execScanPLC(Network Networks[]);
void savePreviousValues(void);

void writeOutputsLocal(void);
void writeOutputsRemote(void);

//--------------------------------------------------------------------------------
// Ladder logic instructions prototypes
// Parameters must match because they are used as array of functions
//--------------------------------------------------------------------------------

void execNop    (int c, int r, int f);
void execConn   (int c, int r, int f);
void execNeg    (int c, int r, int f);
void execNO     (int c, int r, int f);
void execNC     (int c, int r, int f);
void execRE     (int c, int r, int f);
void execFE     (int c, int r, int f);
void execCoil   (int c, int r, int f);
void execCoilL  (int c, int r, int f);
void execCoilU  (int c, int r, int f);
void execTON    (int c, int r, int f);
void execTOFF   (int c, int r, int f);
void execTP     (int c, int r, int f);
void execCTU    (int c, int r, int f);
void execCTD    (int c, int r, int f);
void execMOVE   (int c, int r, int f);
void execSUB    (int c, int r, int f);
void execADD    (int c, int r, int f);
void execMUL    (int c, int r, int f);
void execDIV    (int c, int r, int f);
void execMOD    (int c, int r, int f);
void execSHL    (int c, int r, int f);
void execSHR    (int c, int r, int f);
void execROL    (int c, int r, int f);
void execROR    (int c, int r, int f);
void execAND    (int c, int r, int f);
void execOR     (int c, int r, int f);
void execXOR    (int c, int r, int f);
void execNOT    (int c, int r, int f);
void execEQ     (int c, int r, int f);
void execGT     (int c, int r, int f);
void execGE     (int c, int r, int f);
void execLT     (int c, int r, int f);
void execLE     (int c, int r, int f);
void execNE     (int c, int r, int f);

//--------------------------------------------------------------------------------
// Aux functions for ladder logic instructions data management
//--------------------------------------------------------------------------------

int  GetDataValue     (int r, int c);
int  GetPreviousValue (int r, int c);
void SetDataValue     (int r, int c, int Value);

//--------------------------------------------------------------------------------
// PLC program management functions
//--------------------------------------------------------------------------------

void clearProgram (Network Networks[]);
void loadDemoUserPogram (Network Networks[]);

#endif
