ElPercha/PLsi/firm/test/_test.h

#include <globals.h>
// #include <TFT_eSPI.h>
// #include <hmi.h>

// We need this header file to use FLASH as storage with PROGMEM directive:
#include <pgmspace.h>


      // tft.setSwapBytes(true);
      // tft.pushImage(30, 30, circleWidth, circleHeight, circle);
      // tft.pushImage(10, 100, 100, 100, colorWheel);
      // tft.pushImage(140, 100, 70, 70, iconHome);
      // tft.pushImage(230, 100, 70, 58, home2);
      // tft.pushImage(50, 169, 56, 60, config1);




// Icon width and height
const uint16_t circleWidth = 32;
const uint16_t circleHeight = 32;

const unsigned short  circle[1024] PROGMEM={
0x0000, 0x0000, 0x0000, 0x0000, 0x0000, 0x0000, 0x0000, 0x0000, 0x0000, 0x0000, 0x0000, 0x0000, 0x0000, 0x0000, 0x0000, 0x0000,   // 0x0010 (16) pixels
0x0000, 0x0000, 0x0000, 0x0000, 0x0000, 0x0000, 0x0000, 0x0000, 0x0000, 0x0000, 0x0000, 0x0000, 0x0000, 0x0000, 0x0000, 0x0000,   // 0x0020 (32) pixels
0x0000, 0x0000, 0x0000, 0x0000, 0x0000, 0x0000, 0x0000, 0x0000, 0x0000, 0x0000, 0xAD55, 0xA514, 0xA514, 0xA514, 0xA514, 0xA514,   // 0x0030 (48) pixels
0xA514, 0xA514, 0xA514, 0xA514, 0xA514, 0xAD55, 0x0000, 0x0000, 0x0000, 0x0000, 0x0000, 0x0000, 0x0000, 0x0000, 0x0000, 0x0000,   // 0x0040 (64) pixels
0x0000, 0x0000, 0x0000, 0x0000, 0x0000, 0x0000, 0x0000, 0x0000, 0x9CD3, 0x9CF3, 0xA514, 0xA514, 0xA514, 0xA514, 0xA514, 0xA514,   // 0x0050 (80) pixels
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
0x0000, 0x0000, 0x992A, 0xF9F0, 0xF9F0, 0xF9F0, 0xF9F0, 0xF9F0, 0xF9F0, 0xF9F0, 0xF9F0, 0xF9F0, 0x8908, 0x0000, 0x0000, 0x8189,   // 0x0480 (1152) pixels
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
